DanielKGM/autoponto-firmware/src/Icons.cpp

#include "Icons.h"

// happy_icon - 38x38 RGB565 BIG-ENDIAN
const uint16_t happy_icon[1444] = {
    0x0000,
    0x0000,
    0x0000,
    0x0000,
    0x0000,
    0x0000,
    0x0000,
    0x0000,
    0x0000,
    0x0000,
    0x0000,
    0x0000,
    0x0000,
    0x0000,
    0xFFFF,
    0xFFFF,
    0xFFFF,
    0xFFFF,
    0xFFFF,
    0xFFFF,
    0xFFFF,
    0xFFFF,
    0xFFFF,
    0xFFFF,
    0x0000,
    0x0000,
    0x0000,
    0x0000,
    0x0000,
    0x0000,
    0x0000,
    0x0000,
    0x0000,
    0x0000,
    0x0000,
    0x0000,
    0x0000,
    0x0000,
    0x0000,
    0x0000,
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
};

// sad_icon - 38x38 RGB565 BIG-ENDIAN
const uint16_t sad_icon[1444] = {
    0x0000,
    0x0000,
    0x0000,
    0x0000,
    0x0000,
    0x0000,
    0x0000,
    0x0000,
    0x0000,
    0x0000,
    0x0000,
    0x0000,
    0x0000,
    0x0000,
    0xFFFF,
    0xFFFF,
    0xFFFF,
    0xFFFF,
    0xFFFF,
    0xFFFF,
    0xFFFF,
    0xFFFF,
    0xFFFF,
    0xFFFF,
    0x0000,
    0x0000,
    0x0000,
    0x0000,
    0x0000,
    0x0000,
    0x0000,
    0x0000,
    0x0000,
    0x0000,
    0x0000,
    0x0000,
    0x0000,
    0x0000,
    0x0000,
    0x0000,
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
};

// server_icon - 38x38 RGB565 BIG-ENDIAN
const uint16_t server_icon[1444] = {
    0x0000,
    0xFFFF,
    0xFFFF,
    0xFFFF,
    0xFFFF,
    0xFFFF,
    0xFFFF,
    0xFFFF,
    0xFFFF,
    0xFFFF,
    0xFFFF,
    0xFFFF,
    0xFFFF,
    0xFFFF,
    0xFFFF,
    0xFFFF,
    0xFFFF,
    0xFFFF,
    0xFFFF,
    0xFFFF,
    0xFFFF,
    0xFFFF,
    0xFFFF,
    0xFFFF,
    0xFFFF,
    0xFFFF,
    0xFFFF,
    0xFFFF,
    0xFFFF,
    0xFFFF,
    0xFFFF,
    0xFFFF,
    0xFFFF,
    0xFFFF,
    0xFFFF,
    0xFFFF,
    0xFFFF,
    0x0000,
    0xFFFF,
    0xFFFF,
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
};

// wifi_icon - 38x38 RGB565 BIG-ENDIAN
const uint16_t wifi_icon[1444] = {
    0x0000,
    0x0000,
    0x0000,
    0x0000,
    0x0000,
    0x0000,
    0x0000,
    0x0000,
    0x0000,
    0x0000,
    0x0000,
    0x0000,
    0x0000,
    0x0000,
    0x0000,
    0x0000,
    0x0000,
    0x0000,
    0x0000,
    0x0000,
    0x0000,
    0x0000,
    0x0000,
    0x0000,
    0x0000,
    0x0000,
    0x0000,
    0x0000,
    0x0000,
    0x0000,
    0x0000,
    0x0000,
    0x0000,
    0x0000,
    0x0000,
    0x0000,
    0x0000,
    0x0000,
    0x0000,
    0x0000,
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
};
