DanielKGM/autoponto-firmware/include/MQTT.h

#pragma once
#include <ArduinoJson.h>
#include <PubSubClient.h>

#define MQTT_TOPIC_SIZE 17 // deviceId + '/' + ('log' | 'cmd') + '/0'
#define MQTT_PAYLOAD_MAX 512

namespace mqtt
{
    extern char topicCmd[MQTT_TOPIC_SIZE];
    extern char topicLogs[MQTT_TOPIC_SIZE];

    bool isConnected();
    void publish(const char *topic, const char *payload, bool retain = false);
    bool publishStatus(const char *status);
    void TaskMqttCode(void *pvParameters);
}
