DanielKGM/autoponto-firmware/include/Display.h

#pragma once
#include <JPEGDEC.h>
#include <TFT_eSPI.h>

namespace display
{
    struct Icon
    {
        const uint16_t *data;
        uint16_t width;
        uint16_t height;
        uint32_t color;
    };

    extern const Icon ICON_WIFI;
    extern const Icon ICON_SAD;
    extern const Icon ICON_HAPPY;
    extern const Icon ICON_SERVER;

    bool sendDisplayMessage(const char *text, unsigned long durationMs = 100, const Icon *icon = nullptr);
    bool isFullscreenMessageActive();
    void TaskDisplayCode(void *pvParameters);

    void configTFT();
    void configSprite();
}
